Estevaoassis/Nb-Iot-EspCam/Software/output/foto_mqtt_20260609_004425.jpg

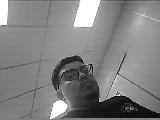
Software/output/foto_mqtt_20260609_004425.jpg
