Estevaoassis/Nb-Iot-EspCam/Software/output/foto_mqtt_20260603_195008.jpg

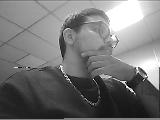
Software/output/foto_mqtt_20260603_195008.jpg
