Estevaoassis/Nb-Iot-EspCam/Software/output/foto_mqtt_20260603_200820.jpg

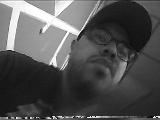
Software/output/foto_mqtt_20260603_200820.jpg
