Estevaoassis/Nb-Iot-EspCam/Software/output/foto_mqtt_20260609_003512.jpg

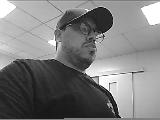
Software/output/foto_mqtt_20260609_003512.jpg
