Estevaoassis/Nb-Iot-EspCam/Software/output/foto_mqtt_20260609_004853.jpg

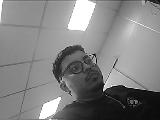
Software/output/foto_mqtt_20260609_004853.jpg
